d3lta-v/SSTuino/docs/tutorials/Sec1/partsList_images/CP2102 MicroB.jpg

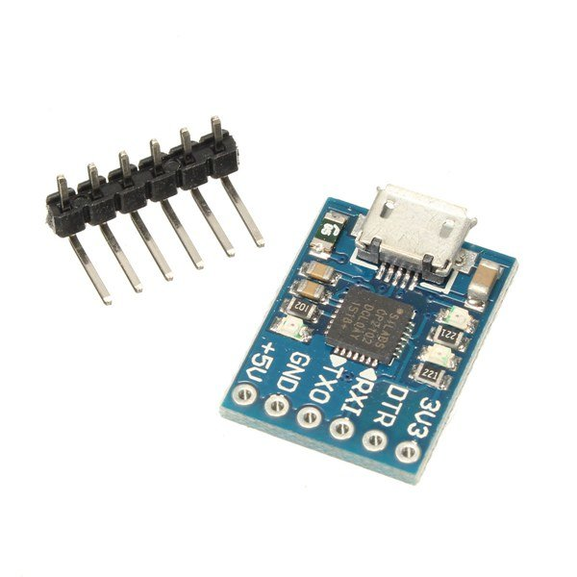
docs/tutorials/Sec1/partsList_images/CP2102 MicroB.jpg
