d3lta-v/SSTuino/docs/tutorials/Sec1/partsList_images/Slide1.PNG

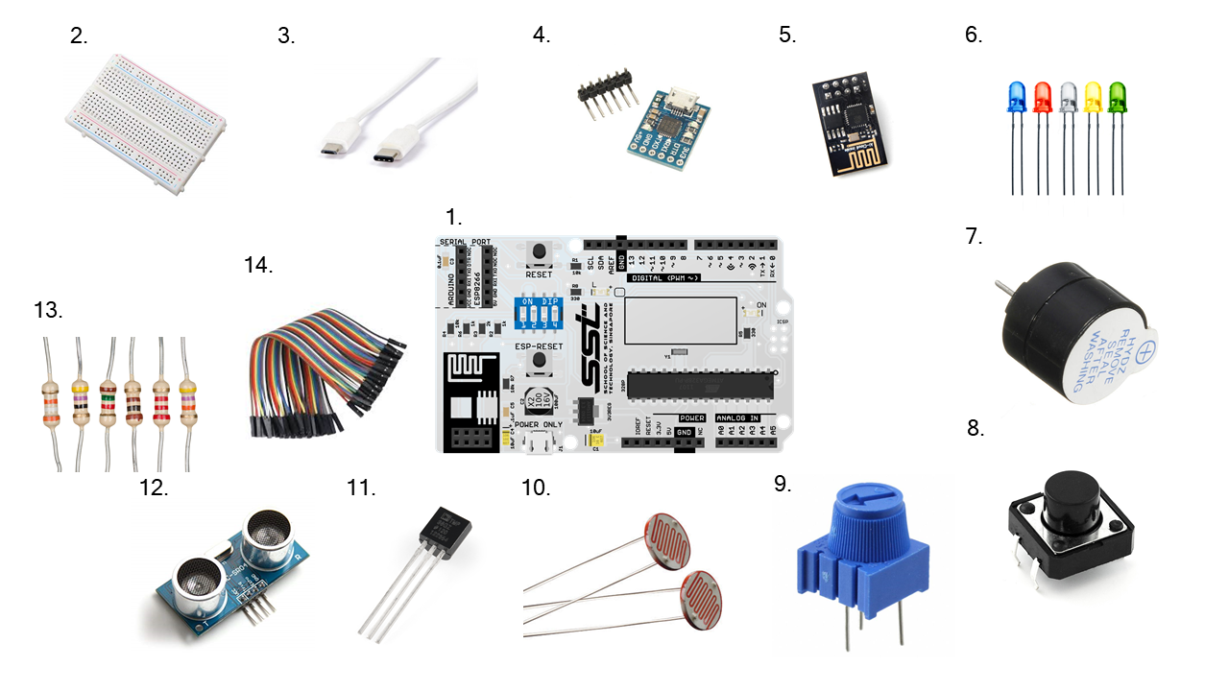
docs/tutorials/Sec1/partsList_images/Slide1.PNG
