d3lta-v/SSTuino/docs/tutorials/Sec1/sstuinoIoT_images/SSTuinoIoT32.png

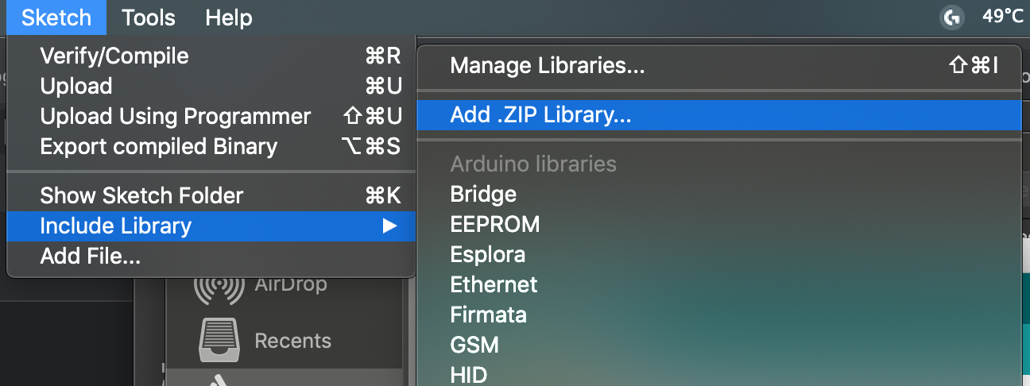
docs/tutorials/Sec1/sstuinoIoT_images/SSTuinoIoT32.png
