d3lta-v/SSTuino/docs/tutorials/Sec1/sstuinoIoT_images/SSTuinoIoT33.png

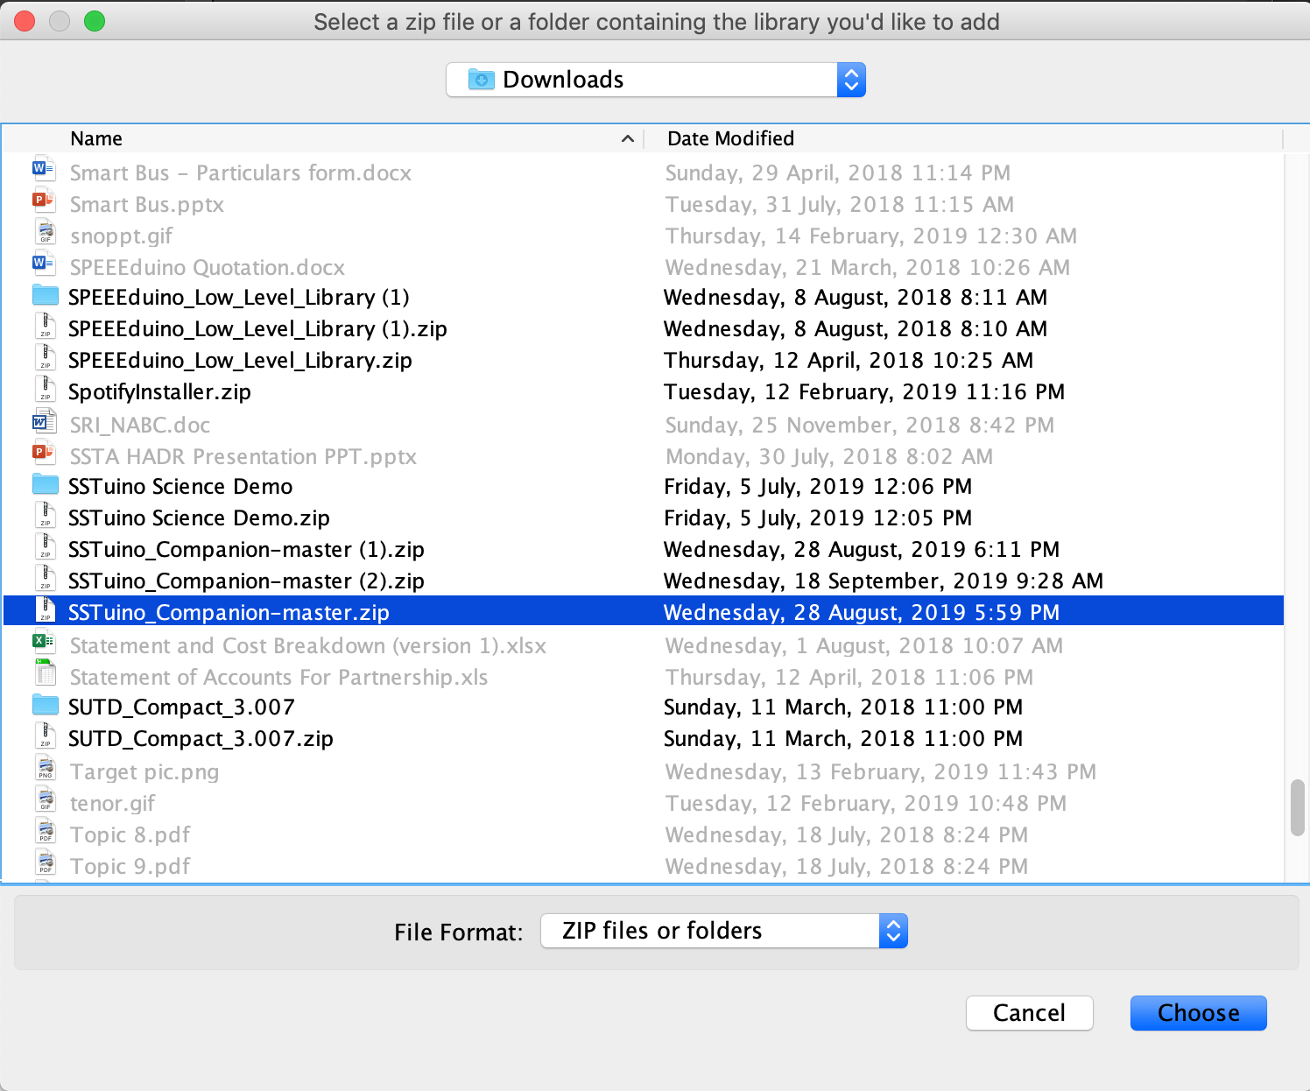
docs/tutorials/Sec1/sstuinoIoT_images/SSTuinoIoT33.png
