d3lta-v/SSTuino/Image Assets/Tutorial Image Assets/1_Resistor/Conections.png

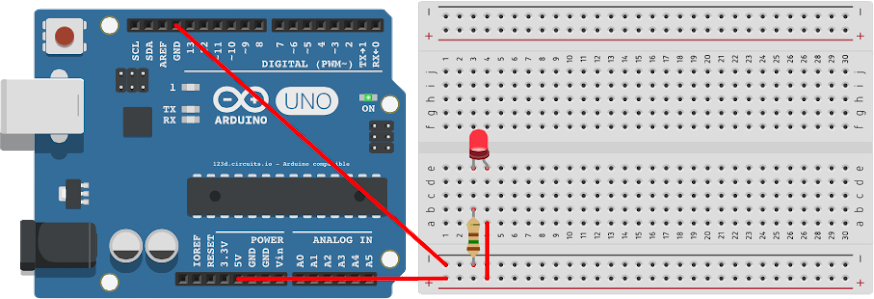
Image Assets/Tutorial Image Assets/1_Resistor/Conections.png
