d3lta-v/SSTuino/Image Assets/Tutorial Image Assets/2_Button/Connections.png

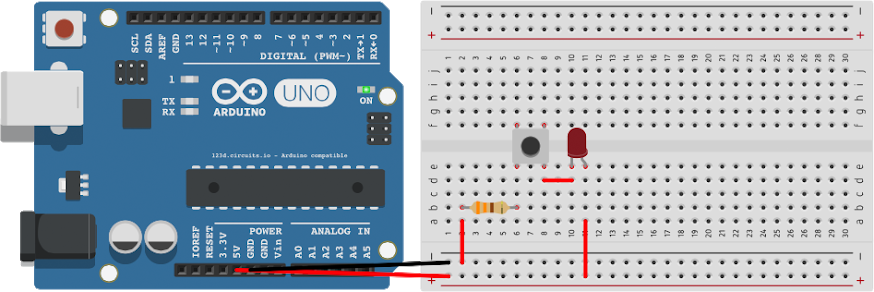
Image Assets/Tutorial Image Assets/2_Button/Connections.png
