d3lta-v/SSTuino/Image Assets/Tutorial Image Assets/3_PinMode/Connections.png

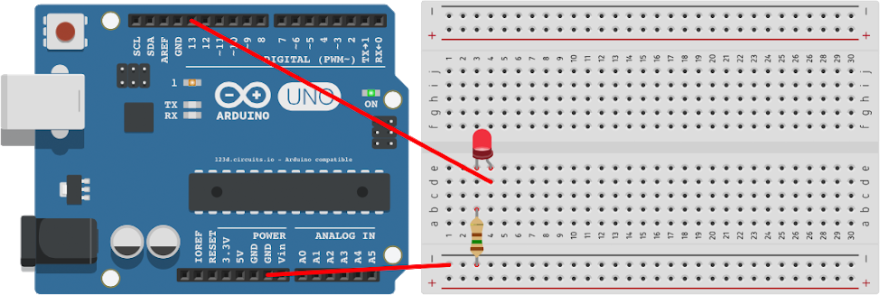
Image Assets/Tutorial Image Assets/3_PinMode/Connections.png
