d3lta-v/SSTuino/Image Assets/Tutorial Image Assets/4_delay/CodeBlock.png

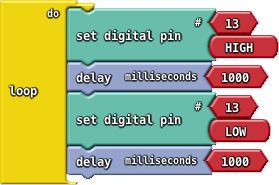
Image Assets/Tutorial Image Assets/4_delay/CodeBlock.png
