d3lta-v/SSTuino/Image Assets/Tutorial Image Assets/5_digitalRead/arduinoButton10.png

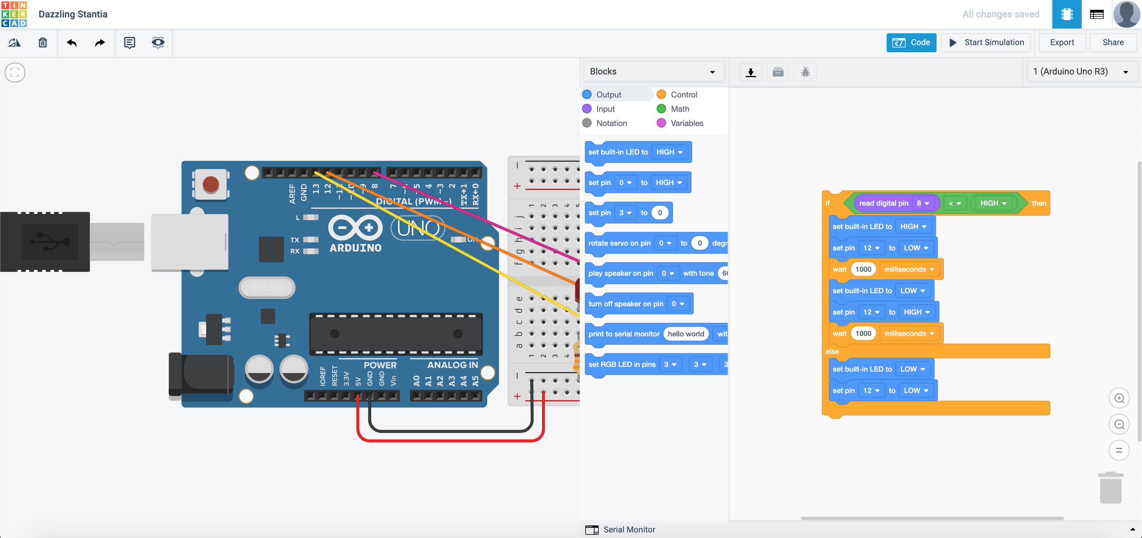
Image Assets/Tutorial Image Assets/5_digitalRead/arduinoButton10.png
