d3lta-v/SSTuino/Image Assets/Tutorial Image Assets/5_digitalRead/boardConnections.png

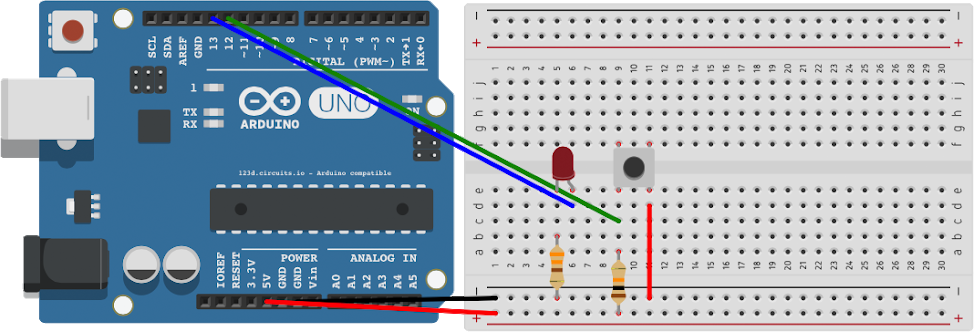
Image Assets/Tutorial Image Assets/5_digitalRead/boardConnections.png
