d3lta-v/SSTuino/Image Assets/Tutorial Image Assets/6_Potentiometer/Connections.png

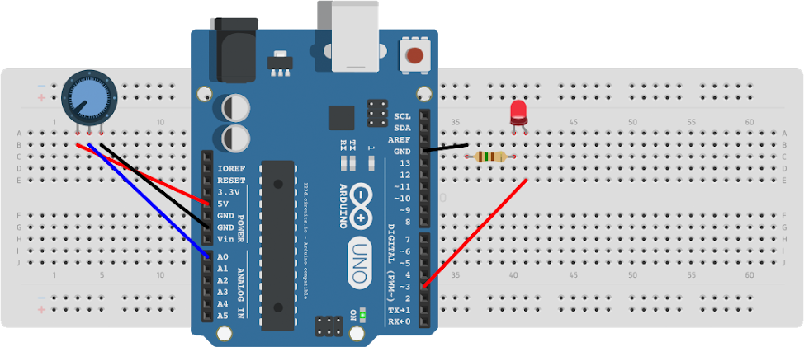
Image Assets/Tutorial Image Assets/6_Potentiometer/Connections.png
