d3lta-v/SSTuino/Image Assets/Tutorial Image Assets/7_buzzer/Connections.png

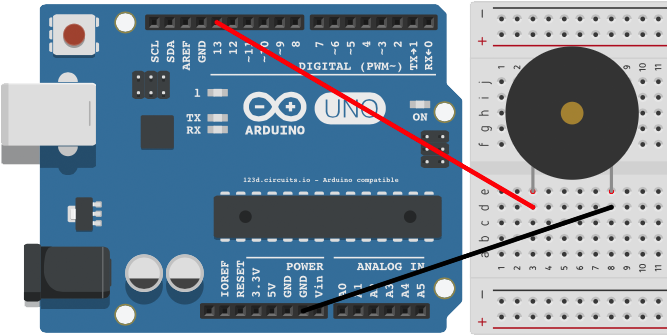
Image Assets/Tutorial Image Assets/7_buzzer/Connections.png
